Sofia-Carrion/Watercolour_Pen_Plotter/Photos/Peg_Down_Sketch.png

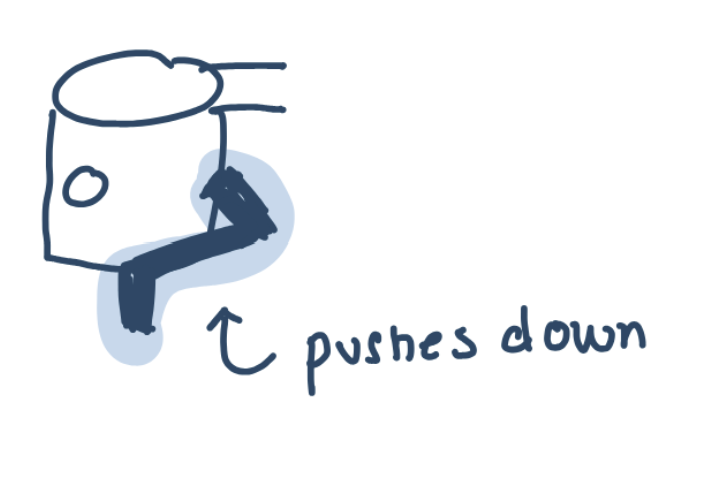
Photos/Peg_Down_Sketch.png
